supermoun62/Projet_Cde_Prise_Chacon_54650Rx/Schema_Cde_Prise_Chacon_54650Rx_V2/Schema_Commande_Chacon_54650TX_V2.pdf

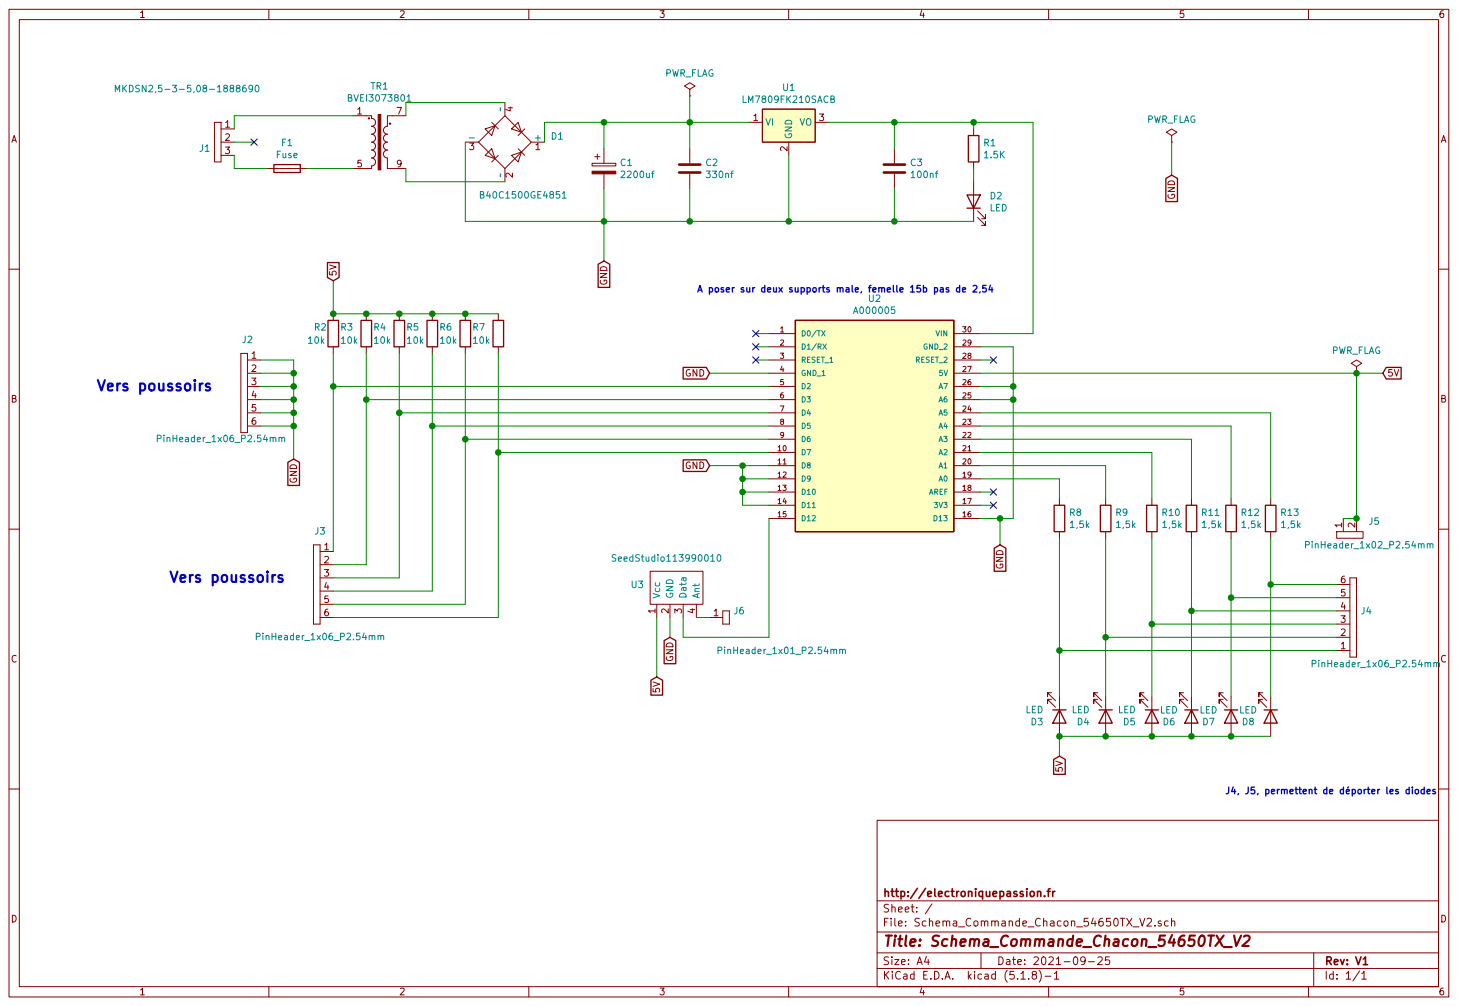
[picture p14: page 1]

A poser sur deux supports male, femelle 15b pas de 2,54

LED | LED D5 | LED | LED | LED

J4, J5, permettent de déporter les diodes

File: Schema_Commande_Chacon_54650TX_V2.sch Sheet: / http://electroniquepassion.fr
