supermoun62/Projet_Cde_Prise_Chacon_54650Rx/PCB_PDF_Commande_Chacon_54650TX_V2/Schema_Commande_Chacon_54650TX_V2-Cmts_User.pdf

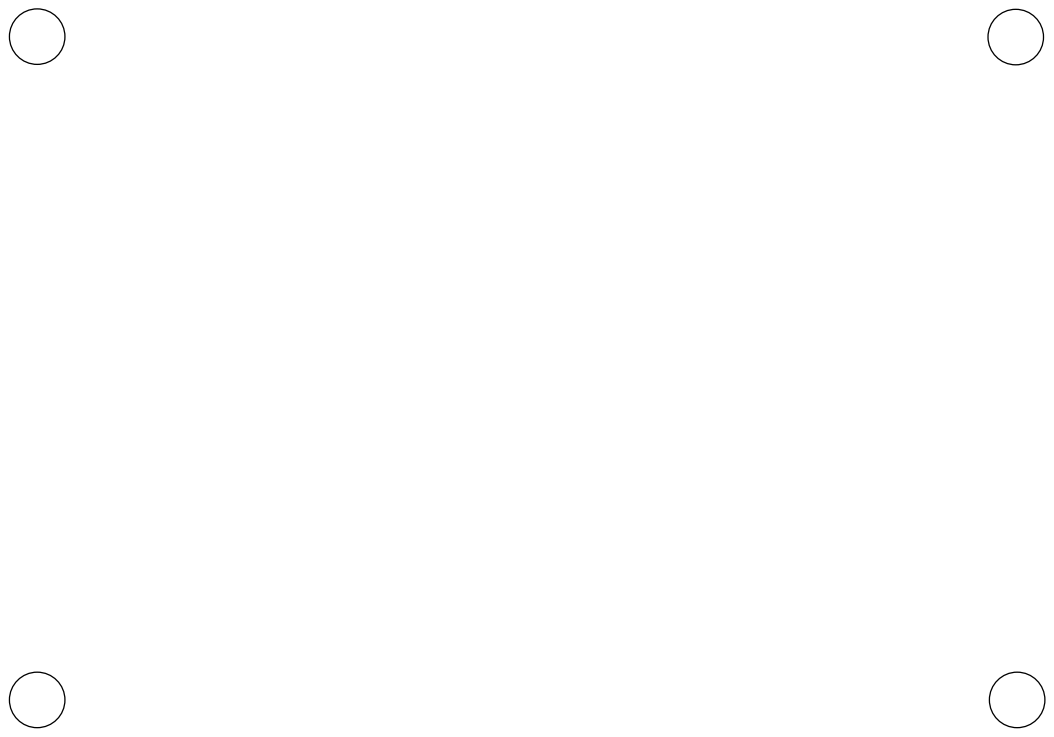
[picture p17: page 1]
