supermoun62/Projet_Cde_Prise_Chacon_54650Rx/Schema_Decodage_Chacon_54650TX/Schema_Decodage_Chacon_54650TX.pdf

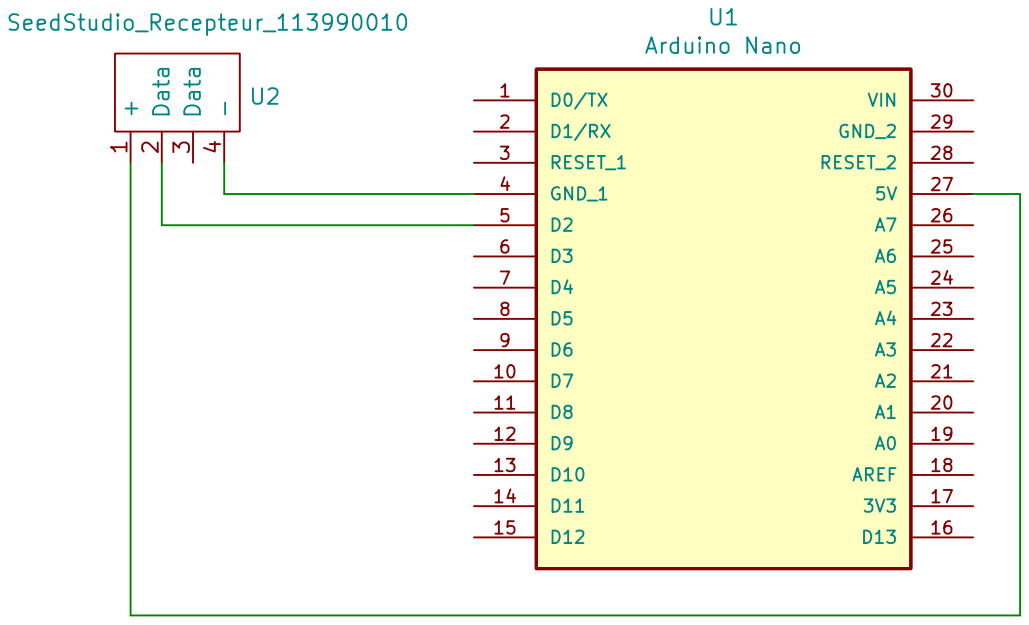
[picture p22: page 1]

File: Schema_Decodage_Chacon_54650TX.sch Sheet: / http://electroniquepassion.fr
