supermoun62/Projet_Cde_Prise_Chacon_54650Rx/ReceiveDemo_Simple/Schema_Cde_Prise_Chacon_54650Rx_V1/Schema_Commande_Chacon_54650TX_V1.pdf

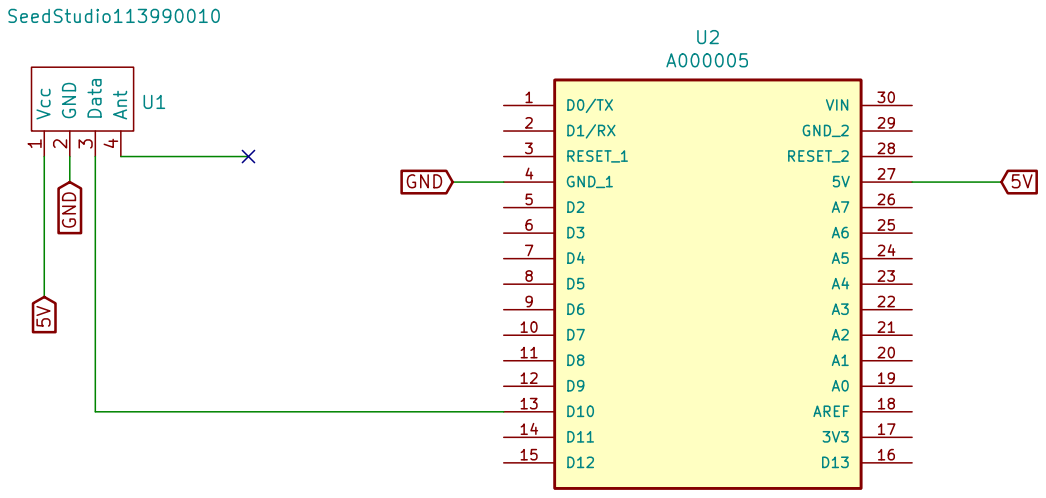
[picture p23: page 1]

File: Schema_Commande_Chacon_54650TX_V1.sch Sheet: / http://electroniquepassion.fr
